matbeedotcom/teensy-ambisonic-microphone-array/teensy_src/AudioOutputTDM_Slave.cpp

/* Audio Library for Teensy 3.X
 * Copyright (c) 2017, Paul Stoffregen, paul@pjrc.com
 * Modified for TDM slave operation
 *
 * Development of this audio library was funded by PJRC.COM, LLC by sales of
 * Teensy and Audio Adaptor boards.  Please support PJRC's efforts to develop
 * open source software by purchasing Teensy or other PJRC products.
 *
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
 * THE SOFTWARE IS PROVIDED "AS IS", WITHOUT WARRANTY OF ANY KIND, EXPRESS OR
 * IMPLIED, INCLUDING BUT NOT LIMITED TO THE WARRANTIES OF MERCHANTABILITY,
 * FITNESS FOR A PARTICULAR PURPOSE AND NONINFRINGEMENT. IN NO EVENT SHALL THE
 * AUTHORS OR COPYRIGHT HOLDERS BE LIABLE FOR ANY CLAIM, DAMAGES OR OTHER
 * LIABILITY, WHETHER IN AN ACTION OF CONTRACT, TORT OR OTHERWISE, ARISING FROM,
 * OUT OF OR IN CONNECTION WITH THE SOFTWARE OR THE USE OR OTHER DEALINGS IN
 * THE SOFTWARE.
 */

#include <Arduino.h>

#if !defined(KINETISL)

#include "AudioOutputTDM_Slave.h"
#include "memcpy_audio.h"
#include "utility/imxrt_hw.h"

audio_block_t * AudioOutputTDM_Slave::block_input[16] = {
	nullptr, nullptr, nullptr, nullptr, nullptr, nullptr, nullptr, nullptr,
	nullptr, nullptr, nullptr, nullptr, nullptr, nullptr, nullptr, nullptr
};
bool AudioOutputTDM_Slave::update_responsibility = false;
DMAChannel AudioOutputTDM_Slave::dma(false);
DMAMEM __attribute__((aligned(32)))
static uint32_t zeros[AUDIO_BLOCK_SAMPLES/2];
DMAMEM __attribute__((aligned(32)))
static uint32_t tdm_tx_buffer[AUDIO_BLOCK_SAMPLES*16];

void AudioOutputTDM_Slave::begin(void)
{
	dma.begin(true);

	for (int i=0; i < 16; i++) {
		block_input[i] = nullptr;
	}
	memset(zeros, 0, sizeof(zeros));
	memset(tdm_tx_buffer, 0, sizeof(tdm_tx_buffer));

	config_tdm_slave();
#if defined(KINETISK)
	CORE_PIN22_CONFIG = PORT_PCR_MUX(6);

	dma.TCD->SADDR = tdm_tx_buffer;
	dma.TCD->SOFF = 4;
	dma.TCD->ATTR = DMA_TCD_ATTR_SSIZE(2) | DMA_TCD_ATTR_DSIZE(2);
	dma.TCD->NBYTES_MLNO = 4;
	dma.TCD->SLAST = -sizeof(tdm_tx_buffer);
	dma.TCD->DADDR = &I2S0_TDR0;
	dma.TCD->DOFF = 0;
	dma.TCD->CITER_ELINKNO = sizeof(tdm_tx_buffer) / 4;
	dma.TCD->DLASTSGA = 0;
	dma.TCD->BITER_ELINKNO = sizeof(tdm_tx_buffer) / 4;
	dma.TCD->CSR = DMA_TCD_CSR_INTHALF | DMA_TCD_CSR_INTMAJOR;
	dma.triggerAtHardwareEvent(DMAMUX_SOURCE_I2S0_TX);

	update_responsibility = update_setup();
	dma.enable();

	I2S0_TCSR = I2S_TCSR_SR;
	I2S0_TCSR = I2S_TCSR_TE | I2S_TCSR_BCE | I2S_TCSR_FRDE;
#elif defined(__IMXRT1062__)
	CORE_PIN7_CONFIG  = 3;

	dma.TCD->SADDR = tdm_tx_buffer;
	dma.TCD->SOFF = 4;
	dma.TCD->ATTR = DMA_TCD_ATTR_SSIZE(2) | DMA_TCD_ATTR_DSIZE(2);
	dma.TCD->NBYTES_MLNO = 4;
	dma.TCD->SLAST = -sizeof(tdm_tx_buffer);
	dma.TCD->DADDR = &I2S1_TDR0;
	dma.TCD->DOFF = 0;
	dma.TCD->CITER_ELINKNO = sizeof(tdm_tx_buffer) / 4;
	dma.TCD->DLASTSGA = 0;
	dma.TCD->BITER_ELINKNO = sizeof(tdm_tx_buffer) / 4;
	dma.TCD->CSR = DMA_TCD_CSR_INTHALF | DMA_TCD_CSR_INTMAJOR;
	dma.triggerAtHardwareEvent(DMAMUX_SOURCE_SAI1_TX);

	update_responsibility = update_setup();
	dma.enable();

	I2S1_RCSR |= I2S_RCSR_RE | I2S_RCSR_BCE;
	I2S1_TCSR = I2S_TCSR_TE | I2S_TCSR_BCE | I2S_TCSR_FRDE;

#endif
	dma.attachInterrupt(isr);
}

static void memcpy_tdm_tx(uint32_t *dest, const uint32_t *src1, const uint32_t *src2)
{
	uint32_t i, in1, in2, out1, out2;

	for (i=0; i < AUDIO_BLOCK_SAMPLES/4; i++) {

		in1 = *src1++;
		in2 = *src2++;
		out1 = (in1 << 16) | (in2 & 0xFFFF);
		out2 = (in1 & 0xFFFF0000) | (in2 >> 16);
		*dest = out1;
		*(dest + 8) = out2;

		in1 = *src1++;
		in2 = *src2++;
		out1 = (in1 << 16) | (in2 & 0xFFFF);
		out2 = (in1 & 0xFFFF0000) | (in2 >> 16);
		*(dest + 16)= out1;
		*(dest + 24) = out2;

		dest += 32;
	}
}

void AudioOutputTDM_Slave::isr(void)
{
	uint32_t *dest;
	const uint32_t *src1, *src2;
	uint32_t i, saddr;

#if defined(KINETISK) || defined(__IMXRT1062__)
	saddr = (uint32_t)(dma.TCD->SADDR);
#endif
	dma.clearInterrupt();
	if (saddr < (uint32_t)tdm_tx_buffer + sizeof(tdm_tx_buffer) / 2) {
		dest = tdm_tx_buffer + AUDIO_BLOCK_SAMPLES*8;
	} else {
		dest = tdm_tx_buffer;
	}
	if (update_responsibility) AudioStream::update_all();

	#if IMXRT_CACHE_ENABLED >= 2
	uint32_t *dc = dest;
	#endif

	for (i=0; i < 16; i += 2) {
		src1 = block_input[i] ? (uint32_t *)(block_input[i]->data) : zeros;
		src2 = block_input[i+1] ? (uint32_t *)(block_input[i+1]->data) : zeros;
		memcpy_tdm_tx(dest, src1, src2);
		dest++;
	}

	#if IMXRT_CACHE_ENABLED >= 2
	arm_dcache_flush_delete(dc, sizeof(tdm_tx_buffer) / 2 );
	#endif

	for (i=0; i < 16; i++) {
		if (block_input[i]) {
			release(block_input[i]);
			block_input[i] = nullptr;
		}
	}
}

void AudioOutputTDM_Slave::update(void)
{
	audio_block_t *prev[16];
	unsigned int i;

	__disable_irq();
	for (i=0; i < 16; i++) {
		prev[i] = block_input[i];
		block_input[i] = receiveReadOnly(i);
	}
	__enable_irq();
	for (i=0; i < 16; i++) {
		if (prev[i]) release(prev[i]);
	}
}

void AudioOutputTDM_Slave::config_tdm_slave(void)
{
#if defined(KINETISK)
	SIM_SCGC6 |= SIM_SCGC6_I2S;
	SIM_SCGC7 |= SIM_SCGC7_DMA;
	SIM_SCGC6 |= SIM_SCGC6_DMAMUX;

	if (I2S0_TCSR & I2S_TCSR_TE) return;
	if (I2S0_RCSR & I2S_RCSR_RE) return;

	I2S0_TMR = 0;
	I2S0_TCR1 = I2S_TCR1_TFW(4);
	I2S0_TCR2 = I2S_TCR2_SYNC(0) | I2S_TCR2_BCP;
	I2S0_TCR3 = I2S_TCR3_TCE;
	I2S0_TCR4 = I2S_TCR4_FRSZ(15) | I2S_TCR4_SYWD(31) | I2S_TCR4_MF | I2S_TCR4_FSE;
	I2S0_TCR5 = I2S_TCR5_WNW(31) | I2S_TCR5_W0W(31) | I2S_TCR5_FBT(31);

	I2S0_RMR = 0;
	I2S0_RCR1 = I2S_RCR1_RFW(4);
	I2S0_RCR2 = I2S_RCR2_SYNC(1) | I2S_TCR2_BCP;
	I2S0_RCR3 = I2S_RCR3_RCE;
	I2S0_RCR4 = I2S_RCR4_FRSZ(15) | I2S_RCR4_SYWD(31) | I2S_RCR4_MF | I2S_RCR4_FSE;
	I2S0_RCR5 = I2S_RCR5_WNW(31) | I2S_RCR5_W0W(31) | I2S_RCR5_FBT(31);

#elif defined(__IMXRT1062__)
	CCM_CCGR5 |= CCM_CCGR5_SAI1(CCM_CCGR_ON);

	if (I2S1_TCSR & I2S_TCSR_TE) return;
	if (I2S1_RCSR & I2S_RCSR_RE) return;

	I2S1_TMR = 0;
	I2S1_TCR1 = I2S_TCR1_RFW(4);
	I2S1_TCR2 = I2S_TCR2_SYNC(0) | I2S_TCR2_BCP;
	I2S1_TCR3 = I2S_TCR3_TCE;
	I2S1_TCR4 = I2S_TCR4_FRSZ(15) | I2S_TCR4_SYWD(31) | I2S_TCR4_MF | I2S_TCR4_FSE;
	I2S1_TCR5 = I2S_TCR5_WNW(31) | I2S_TCR5_W0W(31) | I2S_TCR5_FBT(31);

	I2S1_RMR = 0;
	I2S1_RCR1 = I2S_RCR1_RFW(4);
	I2S1_RCR2 = I2S_RCR2_SYNC(1) | I2S_TCR2_BCP;
	I2S1_RCR3 = I2S_RCR3_RCE;
	I2S1_RCR4 = I2S_RCR4_FRSZ(15) | I2S_RCR4_SYWD(31) | I2S_RCR4_MF | I2S_RCR4_FSE;
	I2S1_RCR5 = I2S_RCR5_WNW(31) | I2S_RCR5_W0W(31) | I2S_RCR5_FBT(31);

	CORE_PIN21_CONFIG = 3;
	CORE_PIN20_CONFIG = 3;
#endif
}

#endif
